0x007E/pmg/PMG.asc

C1: Polcap; 1µ
C2: Polcap; 1µ
C3: Polcap; 1µ
C4: Polcap; 1µ
C5: cap; 100n
C6: Polcap; 47µ
D1: diode; 1N4148
D2: diode; 1N4148
D3: diode; 1N4148
D4: diode; 1N4148
D5: diode; 1N4148
D6: diode; 1N4148
D7: diode; 1N4148
D8: diode; 1N4148
D9: LED; Green
D10: LED; Green
D11: LED; Green
D12: LED; Green
D13: LED; Green
D14: LED; Green
D15: LED; Green
J1: njf
Q1: npn
Q2: npn
Q3: npn
Q4: npn
Q5: npn
Q6: npn
Q7: npn
Q8: npn
Q9: npn
Q10: npn
R1: res; 10k
R2: res; 680
R3: res; 10Meg
R4: res; 39k
R5: res; 10k
R6: res; 470
R7: res; 1Meg
R8: res; 10k
R9: res; 1Meg
R10: res; 10k
R11: res; 10k
R12: res; 10k
R13: res; 10k
R14: res; 10k
R15: res; 10k
R16: res; 10k
R17: res; 1k5
R18: res; 1k5
R19: res; 1k5
R20: res; 1k5
R21: res; 1k5
R22: res; 1k5
R23: res; 1k5
V1: signal; SINE(1 1 10)
V2: voltage; 9
Named nets: 0
.MODEL Green D (IS=93.1P RS=42M N=4.61 BV=4 IBV=10U CJO=2.97P VJ=.75 M=.333 TT=4.32U type=LED)
.tran 1000m
